rheslip/M8-Headless/Images/IMG_2588.JPG

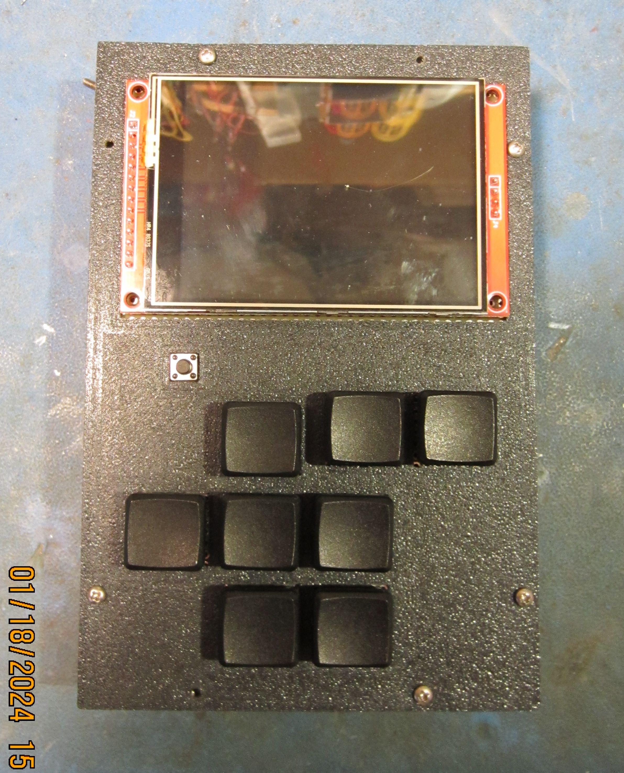
Images/IMG_2588.JPG
