rheslip/M8-Headless/Images/IMG_2589.JPG

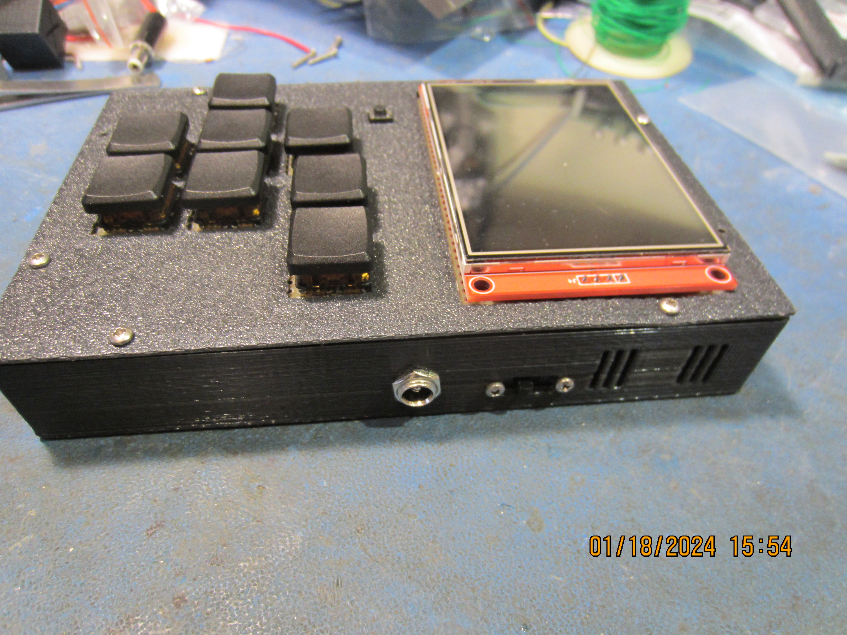
Images/IMG_2589.JPG
