rheslip/M8-Headless/Images/IMG_2590.JPG

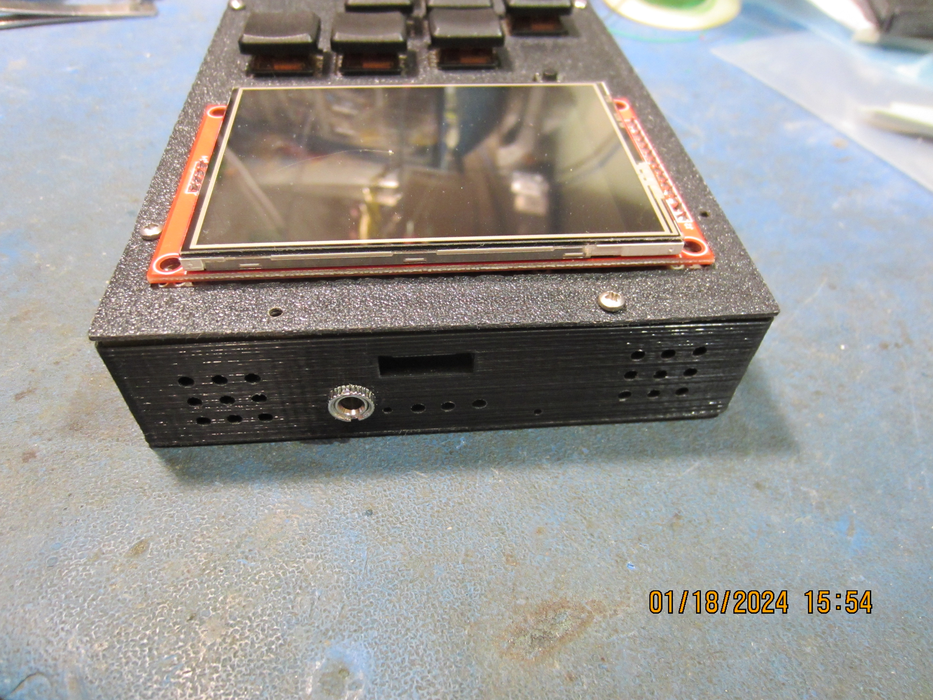
Images/IMG_2590.JPG
