rheslip/M8-Headless/Images/IMG_2591.JPG

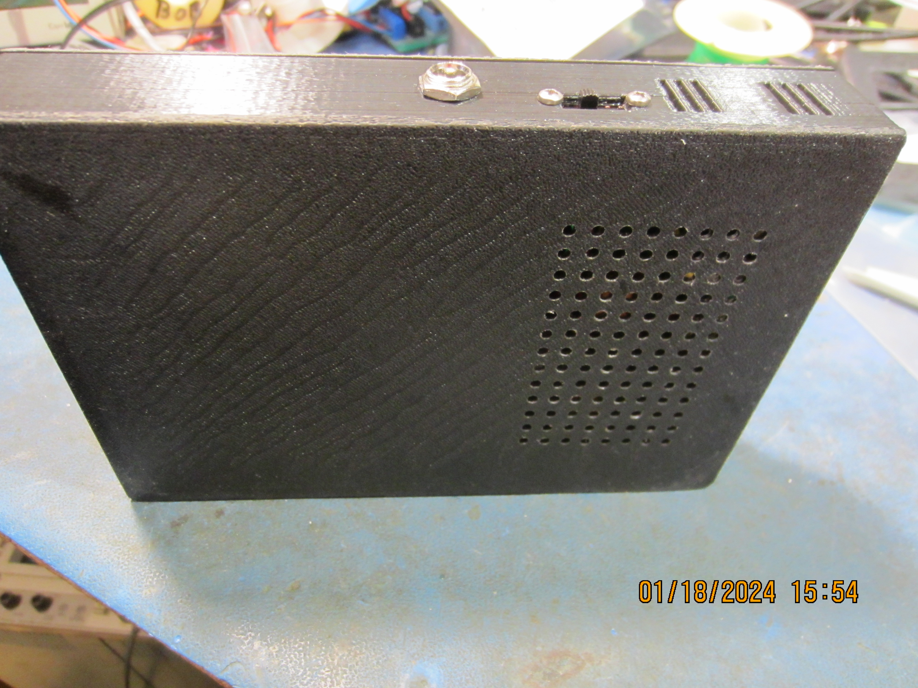
Images/IMG_2591.JPG
