rheslip/M8-Headless/Images/IMG_2593.JPG

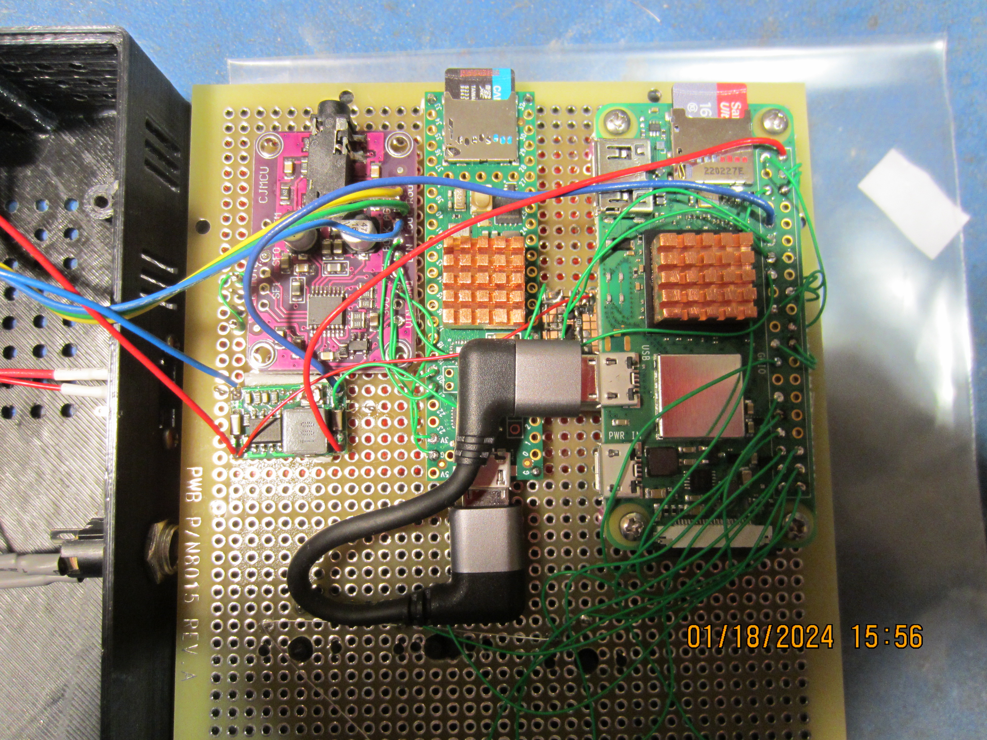
Images/IMG_2593.JPG
